cegan09/VL53L1X_Oil_level_Sender/pictures/4-40 inserts.jpg

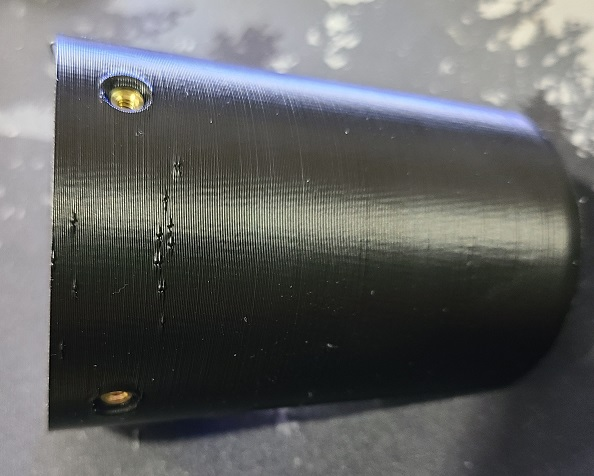
pictures/4-40 inserts.jpg
