cegan09/VL53L1X_Oil_level_Sender/pictures/419vXaiCe-L._AC_.jpg

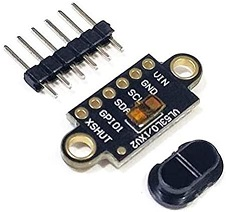
pictures/419vXaiCe-L._AC_.jpg
