cegan09/VL53L1X_Oil_level_Sender/pictures/20220316_091444.jpg

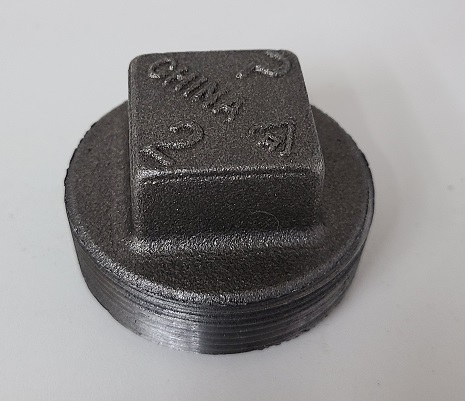
pictures/20220316_091444.jpg
