cegan09/VL53L1X_Oil_level_Sender/pictures/20220316_093203.jpg

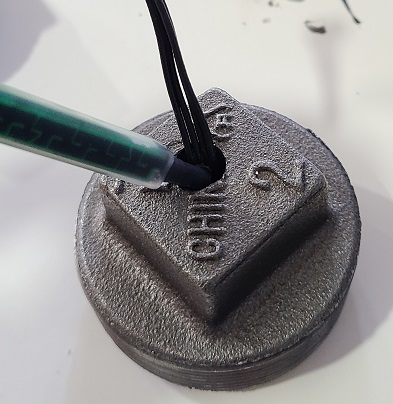
pictures/20220316_093203.jpg
