cegan09/VL53L1X_Oil_level_Sender/pictures/First Light Potting Fill.jpg

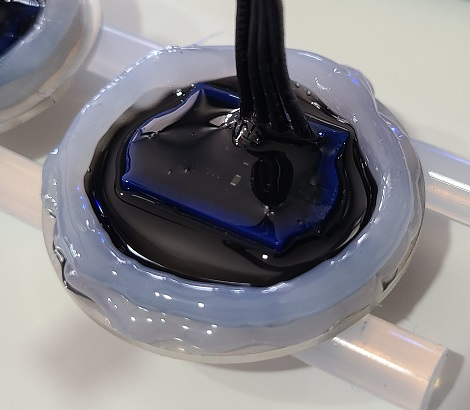
pictures/First Light Potting Fill.jpg
