cegan09/VL53L1X_Oil_level_Sender/pictures/First Potting Layer.jpg

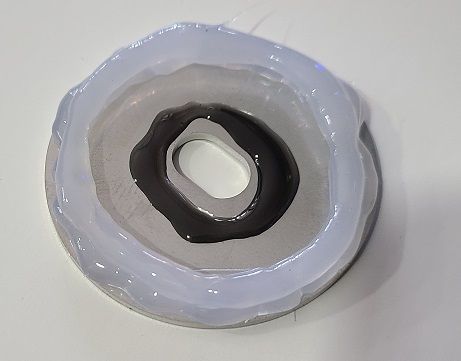
pictures/First Potting Layer.jpg
