cegan09/VL53L1X_Oil_level_Sender/pictures/Isolation Plate.jpg

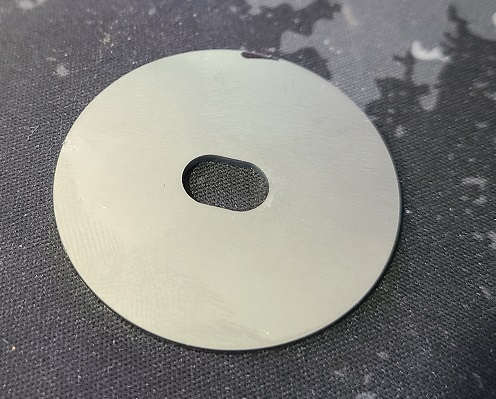
pictures/Isolation Plate.jpg
