cegan09/VL53L1X_Oil_level_Sender/pictures/Sd49a99953e084498abfc570922f9a3c0e.jpg

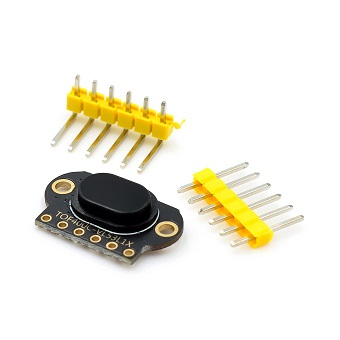
pictures/Sd49a99953e084498abfc570922f9a3c0e.jpg
