cegan09/VL53L1X_Oil_level_Sender/pictures/Sensor Dam.jpg

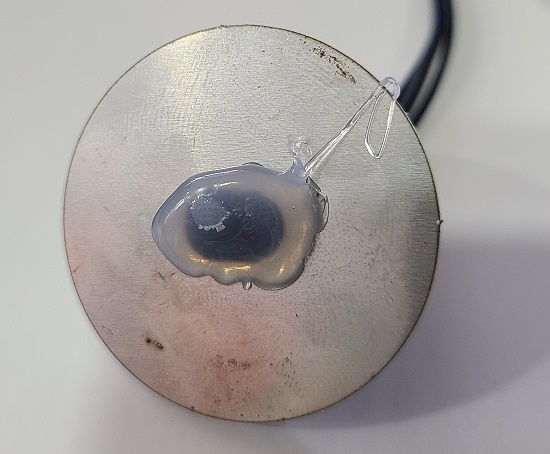
pictures/Sensor Dam.jpg
