cegan09/VL53L1X_Oil_level_Sender/pictures/Sensor Glued in.jpg

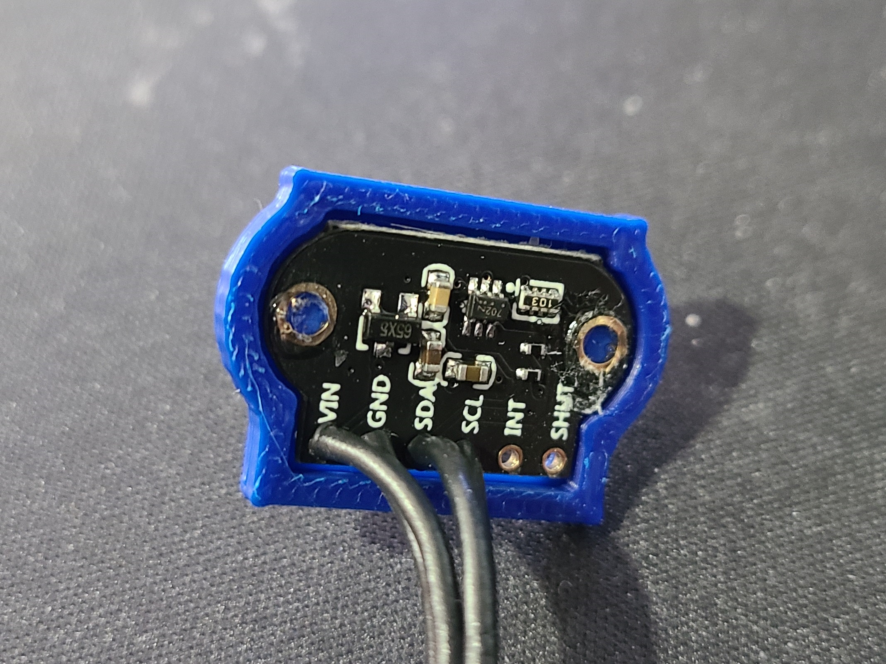
pictures/Sensor Glued in.jpg
