cegan09/VL53L1X_Oil_level_Sender/pictures/Sensor WIred.jpg

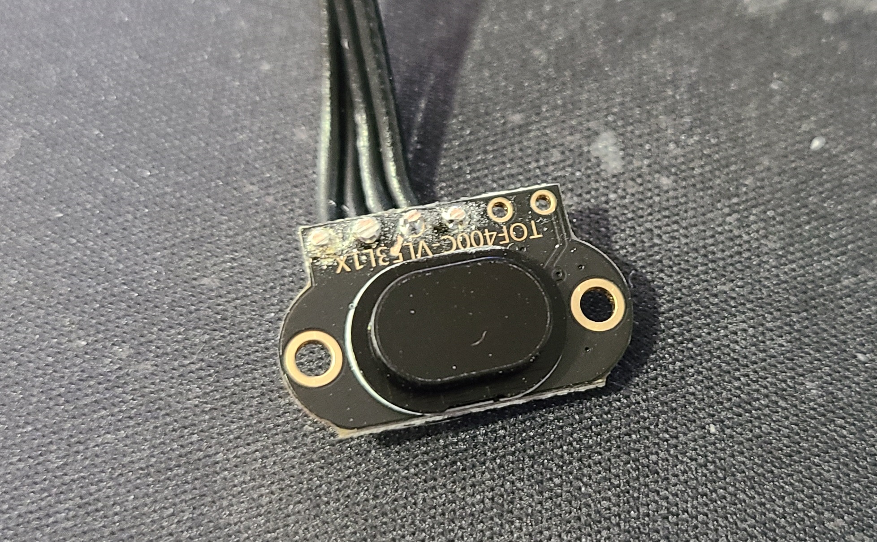
pictures/Sensor WIred.jpg
