cegan09/VL53L1X_Oil_level_Sender/pictures/Sensor Test Fit.jpg

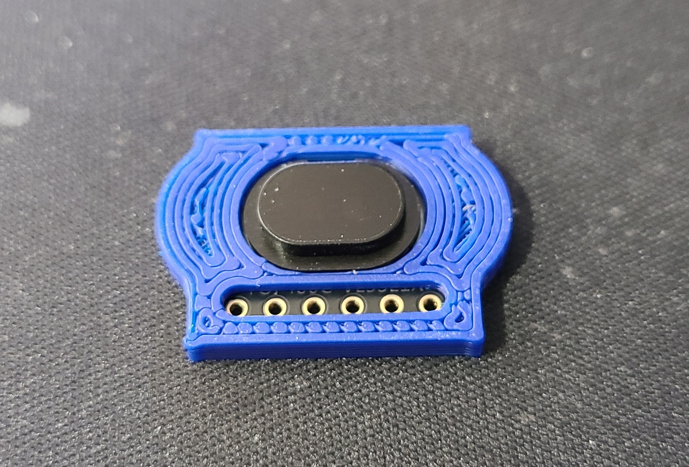
pictures/Sensor Test Fit.jpg
